sparkfun/Proto_Pedal/projects/teensy-based/sims/IO-buffers.asc

C1: cap; 10µ
C2: cap; 10µ
C3: cap; 2.2µ
C4: cap; 1µ
C5: cap; 100p
R1: res; 1meg
R2: res; 10k
R3: res; 1meg
R4: res; 1meg
R5: res; 1meg
R6: res; 22k
R7: res; 10k
R8: res; 1meg
R9: res; 47k
R10: res; 22k
R11: res; 10meg
R12: res; 1meg
U1: UniversalOpamp2
U2: UniversalOpamp2
V1: voltage; SINE(0 1.5 100 1); AC ac 1.
V2: voltage; 9
Named nets: 0
.tran 5
;ac oct 12 1 100k
