sparkfun/Proto_Pedal/projects/gyrator-eq/LT-spice-sim/bass-boost-AC-coupled.asc

C1: cap; 1µ
C2: cap; .47µ
C3: cap; .1µ
C4: cap; 10µ
C5: cap; .05µ
C6: cap; .01µ
C7: cap; 10µ
C8: cap; 100p
NMOS: nmos; Si7540DP_N
R1: res; 10k
R2: res; 10k
R3: res; 10meg
R4: res; 2.2k
R5: res; 2.2k
R6: res; {rv + 1}
R7: res; {10K001 - rv}
R8: res; 10k
R9: res; 10k
R10: res; 1meg
R11: res; 1meg
R12: res; {10k001 - rv}
R13: res; {rv + 1}
R14: res; 2.2k
R15: res; 2.2k
R17: res; 10k
U1: UniversalOpamp2
U2: UniversalOpamp2
U3: UniversalOpamp2
U4: UniversalOpamp2
V1: voltage; 9
V3: voltage; SINE(0 1 100 1); AC AC 1.
Named nets: 0, V+, vout, vref
;tran 0 5 0 startup
.ac oct 12 2 1Meg
.step param rv 1 10K 1k
Gyrator filter parameters:
Assume the R's are equal (R4, R5).
Center frequency is set by R, Cseries (C2), Cinductor (C1)
Q is ration of Cind to Cser
Depth of cut is R vs input/feedback resistors
;.step param rv list 5k 5k001
.inc 5LN01SP.LIB
