sparkfun/Proto_Pedal/projects/gyrator-eq/LT-spice-sim/mosfetfollower.asc

C1: cap; 10n
C2: cap; 10µ
NMOS: nmos; Si7540DP_N
R1: res; 10meg
R2: res; 10meg
R3: res; 100k
R4: res; .00001
R5: res; 20k
V1: voltage; 9; Rser=10
V2: voltage; SINE(0 1 100 1); AC ac 1.
V3: voltage; 4.5
Named nets: 0, Vgen, Vout
.tran 5 startup
;ac oct 12 5 50k
.inc 5LN01SP.LIB
