sparkfun/Proto_Pedal/projects/gyrator-eq/LT-spice-sim/bass-boost.asc

C1: cap; 2µ
C2: cap; 1µ
R1: res; 10k
R2: res; 10k
R4: res; 1k
R5: res; 1k
R6: res; {rv + 1}
R7: res; {10K001 - rv}
U1: UniversalOpamp2
U2: UniversalOpamp2
V1: voltage; 15
V2: voltage; 15
V3: voltage; SINE(0 1 100 1); AC AC 1.
Named nets: 0, V+, V1, vout
;tran 0 5 0 startup
.ac oct 12 2 50k
.step param rv 1 10K 1k
